ostat/gridfinity_extended_openscad/gridfinity_glue_stick.scad

include <modules/module_gridfinity_block.scad>
include <modules/gridfinity_constants.scad>

cup_height = 5;
stick_diameter = 30;
easement_z = 0.7; // a slightly large opening at the top for compliance while inserting.
minimum_wall = 4;

/* [Hidden] */
$fn = 64;
module end_of_customizer_opts() {}

blocks_needed = ceil((stick_diameter+2*minimum_wall)/env_pitch().x);

set_environment(
  width = 1,
  depth = 1,
  height = 2,
  render_position = "center")
glue_stick_cup(blocks_needed, blocks_needed, cup_height);

module glue_stick_cup(num_x=1, num_y=1, num_z=2) {
  difference() {
    grid_block(num_x, num_y, num_z,
      cupBase_settings = CupBaseSettings());
      translate([num_x*env_pitch().x/2, num_y*env_pitch().y/2, 0])
      glue_stick(num_z, stick_diameter);
  }
}

module glue_stick(num_z=5, diam) {
  floor_thickness = blocks_needed > 1 ? 5.5 : 1.2;
  translate([0, 0, floor_thickness]) cylinder(h=num_z*env_pitch().z, d=diam);
  translate([0, 0, (num_z - easement_z)*env_pitch().z + 1.2])
    cylinder(h=easement_z*env_pitch().z, d1=diam, d2=diam*1.1);
}
