ostat/gridfinity_extended_openscad/combined/gridfinity_baseplate.scad

///////////////////////////////////////
//Combined version of 'gridfinity_baseplate.scad'. Generated 2026-09-22 22:52
//Content hash 05C8F93E8DDB1E19475187FF5BAAC2B6E532E4B3174027AFBAF0A886D061BA3F
///////////////////////////////////////
// include instead of use, so we get the pitch

// Plate Style
Base_Plate_Options = "default";//[default:Efficient base, cnclaser:CNC or Laser cut]
// X dimension. grid units (multiples of 42mm) or mm.
Width = [3, 0]; //0.1
// Y dimension. grid units (multiples of 42mm) or mm.
Depth = [2, 0]; //0.1
oversize_method = "fill"; //[crop, fill]
position_fill_grid_x = "near";//[near:"← left", center:"↔ center", far:"→ right"]
position_fill_grid_y = "near";//[far:"↑ up", center:"↕ center", near:"↓ bottom"]
// X outer dimension. grid units (multiples of 42mm) or mm.
outer_Width = [0, 0]; //0.1
// Y outer dimension. grid units (multiples of 42mm) or mm.
outer_Depth = [0, 0]; //0.1
// z outer dimension. mm.
outer_Height = 0; //0.1
position_grid_in_outer_x = "center";//[near:"← left", center:"↔ center", far:"→ right"]
position_grid_in_outer_y = "center";//[far:"↑ up", center:"↕ center", near:"↓ bottom"]
//Reduce the frame wall size to this value
Reduced_Wall_Height = -1; //0.1
Reduced_Wall_Taper = false;
plate_corner_radius = 3.75; //0.01
//Corner radius for the inner corners (Works well with build_plate_enabled)
secondary_corner_radius = 3.75; //0.01

/* [Printer bed options] */
build_plate_enabled = "disabled";//[disabled, enabled, unique]
//spread out the plates, use if last row is small.
average_plate_sizes = false;
//Will split the plate in to the
build_plate_size = [200,250];

/* [Base Plate Options] */
// Enable magnets in the bin corner
Enable_Magnets = false;
//size of magnet, diameter and height. Zacks original used 6.5 and 2.4
Magnet_Size = [6.5, 2.4];  // .1
//raises the magnet, and creates a floor (for gluing)
Magnet_Z_Offset = 0;  // .1
//raises the magnet, and creates a ceiling to capture the magnet
Magnet_Top_Cover = 0;  // .1
// [Magnet Release Options]
// Method to help remove magnets: "none", "slot" (side pry), "hole" (poke from behind)
Magnet_Release_Method = "none"; //[none, slot, hole]
//Enable screws in the bin corner under the magnets
Corner_Screw_Enabled = false;
//Enable hold down screw in the center
Center_Screw_Enabled = false;
//Enable cavity to place frame weights
Enable_Weight = false;
//Removes the bottom taper
Remove_Bottom_Taper = false;

/* [Base Plate Clips]*/
Connector_Only = false;
Connector_Position = "center_wall"; //["center_wall","intersection","both"]

Connector_Clip_Enabled = false;
Connector_Clip_Size = 10;
Connector_Clip_Tolerance = 0.1;

//This feature is not yet finalised, or working properly.
Connector_Butterfly_Enabled = false;
Connector_Butterfly_Size = [5,4,1.5];
Connector_Butterfly_Radius = 0.1;
Connector_Butterfly_Tolerance = 0.1;

//This feature is not yet finalised, or working properly.
Connector_Filament_Enabled = false;
Connector_Filament_Diameter = 2;
Connector_Filament_Length = 8;

//This feature is not yet finalised, or working properly.
Connector_Snaps_Enabled = "disabled"; //["disabled","larger","smaller"]
Connector_Snaps_Clearance = 0.2;

/* [Custom Grid]*/
//Enable custom grid, you will configure this in the (Lid not supported)
Custom_Grid_Enabled = false;

//Custom gid sizes
//I am not sure it this is really useful, but its possible, so here we are.
//0:off the cell is off
//1:on the cell is on and all corners are rounded
//2-16, are bitwise values used to calculate what corners should be rounded, you need to subtract 2 from the value for the bitwise logic (so it does not clash with 0 and 1).
//[c,[x,y]], c corner value as shown above. [x,y] x and y size of the cell.
xpos1 = [3,[2,[3,3]],0,0,2,4,0];
xpos2 = [2,0,0,0,2,2,0];
xpos3 = [2,0,0,0,2,2,0];
xpos4 = [2,2,2,2,2,2,0];
xpos5 = [6,2,2,2,2,10,0];
xpos6 = [0,0,0,0,0,0,0];
xpos7 = [0,0,0,0,0,0,0];

/* [Model detail] */
//Work in progress,  Modify the default grid size. Will break compatibility
pitch = [42,42,7];  //[0:1:9999]
// minimum angle for a fragment (fragments = 360/fa).  Low is more fragments
fa = 6;
// minimum size of a fragment.  Low is more fragments
fs = 0.1;
// number of fragments, overrides $fa and $fs
fn = 0;

/* [debug] */
Render_Position = "center"; //[default,center,zero]
// Debug slice
cut = [0,0,0]; //0.1
// enable loging of help messages during render.
enable_help = false;

/* [Hidden] */
module end_of_customizer_opts() {}
//Combined from path gridfinity_constants.scad


// dimensions as declared on https://gridfinity.xyz/specification/

//Gridfinity grid size
gf_pitch = 42;
//Gridfinity height size
gf_zpitch = 7;

gf_taper_angle = 45;

// cup
gf_cup_corner_radius = 3.75;
gf_cup_floor_thickness = 0.7;  

// CupBase
gf_cupbase_lower_taper_height = 0.8;
gf_cupbase_riser_height = 1.8;
gf_cupbase_upper_taper_height = 2.15;
gf_cupbase_magnet_position = 4.8; 
gf_cupbase_screw_diameter = 3; 
gf_cupbase_screw_depth = 6;
gf_magnet_diameter = 6.5;
gf_magnet_thickness = 2.4;
gf_base_grid_clearance_height = 3.5;

//stacking lips
// Standard lip
// \        gf_lip_upper_taper_height 
//  |       gf_lip_riser_height
//   \      gf_lip_lower_taper_height
//    |     gf_lip_height
//   /      gf_lip_support_taper_height
//  /
// /
///
// Reduced lip
// \        gf_lip_upper_taper_height 
//  |       gf_lip_riser_height
// /        gf_lip_reduced_support_taper_height
/// 
gf_lip_lower_taper_height = 0.7;
gf_lip_riser_height = 1.8;
gf_lip_upper_taper_height = 1.9;
gf_lip_height = 1.2;
//gf_lip_support_taper_height = 2.5;
//gf_lip_reduced_support_taper_height = 1.9;

// base plate
gf_baseplate_lower_taper_height = 0.7;
gf_baseplate_riser_height = 1.8;
gf_baseplate_upper_taper_height = 2.15;
gf_baseplate_magnet_od = 6.5;
gf_baseplate_magnet_thickness = 2.4;

// top lip height 4.4mm
gf_Lip_Height = 4.4-0.6;//gf_lip_lower_taper_height + gf_lip_riser_height + gf_lip_upper_taper_height;

// cupbase height 4.75mm + 0.25.
function gfBaseHeight() = gf_cupbase_lower_taper_height + gf_cupbase_riser_height + gf_cupbase_upper_taper_height+0.25; //results in 5
gf_min_base_height = gfBaseHeight(); 

// base heighttop lip height 4.4mm
function gfBasePlateHeight() = gf_baseplate_lower_taper_height + gf_baseplate_riser_height + gf_baseplate_upper_taper_height;

 

// old names, that will get replaced
/*
gridfinity_lip_height = gf_Lip_Height; 
gridfinity_corner_radius = gf_cup_corner_radius ; 
gridfinity_zpitch = env_pitch().z;
minFloorThickness = gf_cup_floor_thickness;  
const_magnet_height = gf_magnet_thickness;
*/

//Small amount to add to prevent clipping in openSCAD
fudgeFactor = 0.01;

color_cup = "LightSlateGray";
color_divider = "Gainsboro"; //LemonChiffon
color_topcavity = "Green";//"SteelBlue";
color_label = "DarkCyan";
color_cupcavity = "LightGreen"; //IndianRed
color_wallcutout = "SandyBrown";
color_basehole = "DarkSlateGray";
color_base = "DimGray";
color_extension = "lightpink";
color_text = "Yellow"; //Gold
color_cut = "Black";
color_lid = "MediumAquamarine";
//CombinedEnd from path gridfinity_constants.scad
//Combined from path module_gridfinity_block.scad







show_gridfinity_demo = false;
if(show_gridfinity_demo){
  
  grid_block($fn=64);
 
  translate([50,0,0])
  union(){
    frame_cavity($fn=64);

    translate([0,50*3,0])
    frame_cavity(remove_bottom_taper=true,$fn=64);
    
    translate([0,50*4,0])
    frame_cavity(reducedWallHeight=1,$fn=64);
  }
  
  translate([150,0,0])
  union(){
    pad_oversize($fn=64);
    
    translate([0,50,0])
    pad_oversize(extend_down=5,$fn=64);
    
    translate([0,50*2,0])
    pad_oversize(margins=1,$fn=64);
    
    translate([0,50*3,0])
    pad_oversize(remove_bottom_taper=true,$fn=64);
    
    translate([0,50*4,0])
    pad_oversize(render_top=false,$fn=64);
    
    translate([0,50*5,0])
    pad_oversize(render_bottom=false,$fn=64);
  }  
}

// basic block with cutout in top to be stackable, optional holes in bottom
// start with this and begin 'carving'
//grid_block();
module grid_block(
  num_x=1, 
  num_y=2, 
  num_z=2, 
  position = "zero",
  filledin = "disabled", //[disabled, enabled, enabledfilllip]
  wall_thickness = 1.2,
  cupBase_settings = CupBaseSettings(),
  lip_settings = LipSettings(),
  help)
{
  lipHeight = 3.75;

  assert_openscad_version();
  cupBase_settings = ValidateCupBaseSettings(cupBase_settings);

  //Legacy variables.
  magnet_size=cupBase_settings[iCupBase_MagnetSize];
  screw_size=cupBase_settings[iCupBase_ScrewSize];
  hole_overhang_remedy=cupBase_settings[iCupBase_HoleOverhangRemedy];
  box_corner_attachments_only = cupBase_settings[iCupBase_CornerAttachmentsOnly];
  sub_pitch=cupBase_settings[iCupBase_SubPitch];
  flat_base=cupBase_settings[iCupBase_FlatBase];
  center_magnet_size = cupBase_settings[iCupBase_CenterMagnetSize];
    
  outer_size = [env_pitch().x - env_clearance().x, env_pitch().y - env_clearance().y];  // typically 41.5
  block_corner_position = [outer_size.x/2 - env_corner_radius(), outer_size.y/2 - env_corner_radius()];  // need not match center of pad corners

  magnet_position = calculateAttachmentPositions(magnet_size[iCylinderDimension_Diameter], screw_size[iCylinderDimension_Diameter]);
   
  overhang_fix = hole_overhang_remedy > 0 && magnet_size[iCylinderDimension_Diameter] > 0 && screw_size[iCylinderDimension_Diameter] > 0 ? hole_overhang_remedy : 0;
  overhang_fix_depth = 0.3;  // assume this is enough
  
  tz(env_pitch().z*num_z-fudgeFactor*2)
  if(filledin == "enabledfilllip"){
    color(env_colour(color_topcavity))
      tz(-fudgeFactor)
      hull() 
      cornercopy(block_corner_position, num_x, num_y) 
      cylinder(r=env_corner_radius(), h=lipHeight);
  } else {
    
    cupLip(
      num_x = num_x, 
      num_y = num_y, 
      lipStyle = lip_settings[iLipStyle],
      wall_thickness = wall_thickness,
      lip_notches = lip_settings[iLipNotch],
      lip_top_relief_height = lip_settings[iLipTopReliefHeight],
      lip_top_relief_width = lip_settings[iLipTopReliefWidth],
      lip_clip_position = lip_settings[iLipClipPosition],
      lip_non_blocking = lip_settings[iLipNonBlocking],
      align_grid = cupBase_settings[iCupBase_AlignGrid]);
  }
  
  translate(gridfinityRenderPosition(position,num_x,num_y))
  difference() {
    baseHeight = 5;
    intersection() {
      //Main cup outer shape
      color(env_colour(color_cup))
        tz(-fudgeFactor)
        hull() 
        cornercopy(block_corner_position, num_x, num_y) 
        cylinder(r=env_corner_radius(), h=env_pitch().z*num_z);

      union(){
        if(flat_base == FlatBase_rounded){
          basebottomRadius = let(fbr = cupBase_settings[iCupBase_FlatBaseRoundedRadius])
            fbr == -1 ? env_corner_radius()/2 : fbr;

          color(env_colour(color_cup))
          translate([env_clearance().x/2,env_clearance().y/2,0])
          roundedCube(
            x = num_x*env_pitch().x-env_clearance().x,
            y = num_y*env_pitch().y-env_clearance().y,
            z = env_pitch().z,
            size=[],
            topRadius = 0,
            bottomRadius = basebottomRadius,
            sideRadius = env_corner_radius(),
            centerxy = false,
            supportReduction_z = [cupBase_settings[iCupBase_FlatBaseRoundedEasyPrint],0]
            );
        } else {
          // logic for constructing odd-size grids of possibly half-pitch pads
          color(env_colour(color_base))
            pad_grid(
              num_x = num_x, 
              num_y = num_y, 
              sub_pitch = sub_pitch, 
              flat_base = flat_base, 
              cupBase_settings[iCupBase_MinimumPrintablePadSize],
              pitch=env_pitch(), 
              positionGridx = cupBase_settings[iCupBase_AlignGrid].x,
              positionGridy = cupBase_settings[iCupBase_AlignGrid].y);
        }

        color(env_colour(color_cup))
        tz(baseHeight) 
          cube([env_pitch().x*num_x, env_pitch().y*num_y, env_pitch().z*num_z]);
      }
    }
    
    color(env_colour(color_cup))
    bin_overhang_chamfer(
      num_x = num_x,
      num_y = num_y,
      baseHeight = baseHeight,
      wall_thickness = wall_thickness,
      corner_radius = env_corner_radius(),
      block_corner_position=block_corner_position,
      cupBase_settings = cupBase_settings);
   
    if(center_magnet_size[iCylinderDimension_Diameter]){
      //Center Magnet
      for(x =[0:1:num_x-1])
      {
        for(y =[0:1:num_y-1])
        {
          color(env_colour(color_basehole))
            translate([
               x * env_pitch().x + env_pitch().x / 2, // Add half pitch in X
               y * env_pitch().y + env_pitch().y / 2, // Add half pitch in Y
               -fudgeFactor
            ])
            cylinder(h=center_magnet_size[iCylinderDimension_Height]-fudgeFactor, d=center_magnet_size[iCylinderDimension_Diameter]);
        }
      }
    }
    
    color(env_colour(color_basehole))
    tz(-fudgeFactor)
    gridcopycorners(num_x, num_y, magnet_position, box_corner_attachments_only){
        magnet_rotation =
          $gcci[2] == [ 1, 1] ? 90 :
          $gcci[2] == [-1, 1] ? 180 :
          $gcci[2] == [-1,-1] ? 270 :
          $gcci[2] == [ 1,-1] ? 0 : 0;
        magnetCaptiveSideAccessSize = magnet_rotation == 0 || magnet_rotation == 180 
          ? env_pitch().x/2 - magnet_position.x 
          : env_pitch().y/2 - magnet_position.y;
        rotate([0,0,magnet_rotation-45])
        MagnetAndScrewRecess(
          magnetDiameter = magnet_size[iCylinderDimension_Diameter],
          magnetThickness = magnet_size[iCylinderDimension_Height]+0.1,
          screwDiameter = screw_size[iCylinderDimension_Diameter],
          screwDepth = screw_size[iCylinderDimension_Height],
          overhangFixLayers = overhang_fix,
          overhangFixDepth = overhang_fix_depth,
          easyMagnetRelease = cupBase_settings[iCupBase_MagnetEasyRelease] == MagnetEasyRelease_off ? false : 
                              cupBase_settings[iCupBase_MagnetCaptiveHeight] > 0 && cupBase_settings[iCupBase_MagnetSideAccess] == false ? false : true,
          magnetCaptiveHeight = cupBase_settings[iCupBase_MagnetCaptiveHeight],
          easyReleaseRotation = (cupBase_settings[iCupBase_NormalisedMagnetEasyRelease] == MagnetEasyRelease_outer ? 0 : 180),
          magnetRotation = magnet_rotation,
          enableSideAccess = cupBase_settings[iCupBase_MagnetSideAccess],
          magnetCaptiveSideAccessSize = [magnetCaptiveSideAccessSize, magnet_size[iCylinderDimension_Diameter], magnet_size[iCylinderDimension_Height]+0.1],
          magnetCrushDepth = cupBase_settings[iCupBase_MagnetCrushDepth],
          magnetChamfer = cupBase_settings[iCupBase_MagnetChamfer]
        );
    }
  }
 
  HelpTxt("grid_block",[
    "num_x",num_x
    ,"num_y",num_y
    ,"num_z",num_z
    ,"magnet_size",magnet_size
    ,"screw_size",screw_size
    ,"position",position
    ,"hole_overhang_remedy",hole_overhang_remedy
    ,"sub_pitch",sub_pitch
    ,"box_corner_attachments_only",box_corner_attachments_only
    ,"flat_base",flat_base
    ,"lipSettings",lip_settings
    ,"filledin",filledin]
    ,help);
}

//TODO: be better if we could round the corners of the chamfer around the bin.
module bin_overhang_chamfer(
  num_x,
  num_y,
  baseHeight,
  wall_thickness,
  corner_radius,
  block_corner_position,
  cupBase_settings = []){
  fudgeFactor = 0.01;

  alignGrid = cupBase_settings[iCupBase_AlignGrid];
  cavityFloorRadius = cupBase_settings[iCupBase_CavityFloorRadius];
  efficientFloor = cupBase_settings[iCupBase_EfficientFloor];
  sub_pitch = cupBase_settings[iCupBase_SubPitch];
  minimumPrintablePadSize = cupBase_settings[iCupBase_MinimumPrintablePadSize];

  calculate_bin_chamfer = function (
    width,
    pitch,
    clearance,
    wallThickness,
    cavityFloorRadius,
    efficientFloor,
    subPitch,
    minimumPrintablePadSize) 
    let(
      over_hanging_lip = (width*subPitch-floor(width*subPitch))/subPitch,
      over_hanging_lip_mm = (over_hanging_lip)*pitch-clearance/4,
      calculatedCavityFloorRadius = calculateCavityFloorRadius(cavityFloorRadius, wallThickness, efficientFloor),
      outer_wall_radius = calculatedCavityFloorRadius + wallThickness*2,
      large_h = sqrt(2 * outer_wall_radius ^ 2),
      small_h = (large_h - outer_wall_radius) * 2,
      max_chamfer = sqrt((small_h^2) / 2),
      correctable_lip = max(0, min(over_hanging_lip_mm, max_chamfer)))
    over_hanging_lip > 0 && over_hanging_lip < minimumPrintablePadSize ? correctable_lip : 0;

    chamfer_lip_x = calculate_bin_chamfer(
      width = num_x,
      pitch = env_pitch().x,
      clearance = env_clearance().x,
      wallThickness = wall_thickness,
      cavityFloorRadius = cavityFloorRadius,
      efficientFloor = efficientFloor,
      subPitch = sub_pitch,
      minimumPrintablePadSize = minimumPrintablePadSize
    );

    chamfer_lip_y = calculate_bin_chamfer(
      width = num_y,
      pitch = env_pitch().y,
      clearance = env_clearance().x,
      wallThickness = wall_thickness,
      cavityFloorRadius = cavityFloorRadius,
      efficientFloor = efficientFloor,
      subPitch = sub_pitch,
      minimumPrintablePadSize = minimumPrintablePadSize
    );

  chamfer_max= max(chamfer_lip_x, chamfer_lip_y);
  lower_radius = env_corner_radius() - chamfer_max;
  echo("bin_overhang_chamfer", num_x=num_x, num_y=num_y, chamfer_lip_x=chamfer_lip_x, chamfer_lip_y=chamfer_lip_y, chamfer_max=chamfer_max, lower_radius=lower_radius);
  if(chamfer_lip_x > 0 || chamfer_lip_y > 0)
  translate([0,0,baseHeight-fudgeFactor])
  difference() {
    cube([env_pitch().x*num_x, env_pitch().y*num_y, chamfer_max]);

    hull() 
      cornercopy(block_corner_position, num_x, num_y)
        union(){
          _translate = [
                cupBase_settings[iCupBase_AlignGrid].x == "far"
                  ? ($idx[0] == 0 ? -((-chamfer_lip_x)+env_clearance().x/4) : -env_clearance().x/4)
                  : ($idx[0] == 0 ? -env_clearance().x/4 : (-chamfer_lip_x)+env_clearance().x/4),
                cupBase_settings[iCupBase_AlignGrid].y == "far"
                  ? ($idx[1] == 0 ? -((-chamfer_lip_y)+env_clearance().y/4) : -env_clearance().y/4)
                  : ($idx[1] == 0 ? -env_clearance().y/4 : (-chamfer_lip_y)+env_clearance().y/4),
                -fudgeFactor];
        hull(){
            translate([0,0,chamfer_max+fudgeFactor*2])
            cylinder(r=env_corner_radius()+fudgeFactor, h=fudgeFactor);
            translate(_translate)
            cylinder(r=env_corner_radius()+fudgeFactor, h=fudgeFactor);
          }
        }
    
  }
}
//CombinedEnd from path module_gridfinity_block.scad
//Combined from path module_gridfinity.scad














module pad_grid(
  num_x, 
  num_y, 
  sub_pitch=1, 
  flat_base="off", 
  minimium_size = 0.2,
  pitch=env_pitch(), 
  positionGridx = "near", 
  positionGridy = "near") {
  assert(is_num(num_x));
  assert(is_num(num_y));
  assert(is_num(sub_pitch));
  assert(is_string(flat_base));
  assert(is_num(minimium_size));

  render_top = true;
  render_bottom = true;
  //echo("pad_grid", flat_base=flat_base, sub_pitch=sub_pitch, positionGridx=positionGridx, positionGridy=positionGridy, minimium_size=minimium_size);
  pad_copy(
    num_x = num_x, 
    num_y = num_y, 
    sub_pitch = sub_pitch, 
    flat_base = flat_base, 
    minimium_size = minimium_size,
    pitch=pitch, 
    positionGridx = positionGridx, 
    positionGridy = positionGridy)
      pad_oversize(
          $pad_copy_size.x, 
          $pad_copy_size.y,
          render_top=render_top,
          render_bottom=render_bottom);
}

// like a cylinder but produces a square solid instead of a round one
// specified 'diameter' is the side length of the square, not the diagonal diameter
module cylsq(d, h) {
  translate([-d/2, -d/2, 0]) cube([d, d, h]);
}

// like a tapered cylinder with two diameters, but square instead of round
module cylsq2(d1, d2, h) {
  linear_extrude(height=h, scale=d2/d1)
  square([d1, d1], center=true);
}

module frame_additives(
  num_x = 2, 
  num_y = 1, 
  position_fill_grid_x = "near",
  position_fill_grid_y = "near",
  render_top = true,
  render_bottom = true,
  remove_bottom_taper = false,
  extra_down=0, 
  frameLipHeight = 4,
  cornerRadius = gf_cup_corner_radius,
  reducedWallHeight = -1,
  reducedWallWidth = -1,
  reducedWallOuterEdgesOnly=false,
  enable_grippers = false) {

  assert(is_num(num_x));
  assert(is_num(num_y));
  assert(is_string(position_fill_grid_x));
  assert(is_string(position_fill_grid_y));
  assert(is_bool(render_top));
  assert(is_bool(render_bottom));
  assert(is_bool(remove_bottom_taper));
  assert(is_num(extra_down));
  assert(is_num(frameLipHeight));
  assert(is_num(cornerRadius));
  assert(is_num(reducedWallHeight));
  assert(is_num(reducedWallWidth));
  assert(is_bool(reducedWallOuterEdgesOnly));
  assert(is_bool(enable_grippers));

  frameWallReduction = reducedWallHeight >= 0 ? max(0, frameLipHeight-reducedWallHeight) : -1;
  if(env_help_enabled("debug")) echo("frame_addatives", childres = $children);
      
    translate([0, 0, -fudgeFactor]) 
      gridcopy(
        num_x, 
        num_y,
        positionGridx = position_fill_grid_x,
        positionGridy = position_fill_grid_y) {
      if($gc_size.x > 0.2 && $gc_size.y >= 0.2){
        
        //wall reducers, cutouts and clips
        children();
    }
  }
}


module frame_cavity(
  num_x = 2, 
  num_y = 1, 
  position_fill_grid_x = "near",
  position_fill_grid_y = "near",
  render_top = true,
  render_bottom = true,
  remove_bottom_taper = false,
  extra_down=0, 
  frameLipHeight = 4,
  cornerRadius = gf_cup_corner_radius,
  reducedWallHeight = -1,
  reducedWallWidth = -1,
  reducedWallOuterEdgesOnly=false,
  enable_grippers = false) {

  assert(is_num(num_x));
  assert(is_num(num_y));
  assert(is_string(position_fill_grid_x));
  assert(is_string(position_fill_grid_y));
  assert(is_bool(render_top));
  assert(is_bool(render_bottom));
  assert(is_bool(remove_bottom_taper));
  assert(is_num(extra_down));
  assert(is_num(frameLipHeight));
  assert(is_num(cornerRadius));
  assert(is_num(reducedWallHeight));
  assert(is_num(reducedWallWidth));
  assert(is_bool(reducedWallOuterEdgesOnly));
  assert(is_bool(enable_grippers));

  frameWallReduction = reducedWallHeight >= 0 ? max(0, frameLipHeight-reducedWallHeight) : -1;

    translate([0, 0, -fudgeFactor]) 
      gridcopy(
        num_x, 
        num_y,
        positionGridx = position_fill_grid_x,
        positionGridy = position_fill_grid_y) {
      if($gc_size.x > 0.2 && $gc_size.y >= 0.2){
        if(frameWallReduction>=0)
          for(side=[[0, [$gc_size.x, $gc_size.y]*env_pitch().x, "x"],[90, [$gc_size.y, $gc_size.x]*env_pitch().y, "y"]]){
            if(side[1].x >= env_pitch().x/2)
            if(!reducedWallOuterEdgesOnly || ($gc_is_corner[1] && side[2] =="x") || ($gc_is_corner[0] && side[2] =="y"))
            translate([$gc_size.x/2*env_pitch().x,$gc_size.y/2*env_pitch().y,frameLipHeight])
            rotate([0,0,side[0]])
              WallCutout(
                lowerWidth=side[1].x-(reducedWallWidth > 0 ? reducedWallWidth*2 : 20),
                wallAngle=80,
                height=frameWallReduction,
                thickness=side[1].y+fudgeFactor*2,
                cornerRadius=frameWallReduction,
                topHeight=1);
              }

      //wall reducers, cutouts and clips
      if($children >=2) children(1);

      pad_oversize(
        num_x=$gc_size.x,
        num_y=$gc_size.y,
        margins=1,
        extend_down=extra_down,
        render_top=render_top,
        render_bottom=render_bottom,
        remove_bottom_taper=remove_bottom_taper)
          //cell cavity
          if($children >=1) children(0);
    }
  }
}

// unit pad slightly oversize at the top to be trimmed or joined with other feet or the rest of the model
// also useful as cutouts for stacking
//pad_oversize(margins=1,extend_down=5, $fn=64);
module pad_oversize(
  num_x=1, 
  num_y=1, 
  margins=0,
  render_top = true,
  render_bottom = true,
  remove_bottom_taper = false,
  extend_down = 0) {
  
  assert(!is_undef(num_x), "num_x is undefined");
  assert(is_num(num_x), "num_x must be a number");
  assert(!is_undef(num_y), "num_y is undefined");
  assert(is_num(num_y), "num_y must be a number");
  assert(!is_undef(margins), "margins is undefined");
  assert(is_num(margins), "margins must be a number >= 0");
  assert(!is_undef(extend_down), "extend_down is undefined");
  assert(is_num(extend_down), "extend_down must be a number >= 0");
  
  if(env_help_enabled("trace")) echo("pad_oversize", num_x=num_x, num_y=num_y, margins= margins);

  // pad_corner_position = [env_pitch().x/2 - 4,env_pitch().y/2 - 4]; 
  // must be 17 to be compatible
  pad_corner_position = [
    env_pitch().x/2-env_corner_radius()-env_clearance().x/2, 
    env_pitch().y/2-env_corner_radius()-env_clearance().y/2];

  bevel1_top = 0.8;     // z of top of bottom-most bevel (bottom of bevel is at z=0)
  bevel2_bottom = 2.6;  // z of bottom of second bevel
  bevel2_top = 5;       // z of top of second bevel
  bonus_ht = 0.2;       // extra height (and radius) on second bevel
  
  // female parts are a bit oversize for a nicer fit
  radialgap = margins ? 0.25 : 0;  // oversize cylinders for a bit of clearance
  //axialdown = margins ? 0.1 : 0;   // a tiny bit of axial clearance present in Zack's design
  //remove axialdown as it messes up the placement of the attachements 
  axialdown =0;
  fudgeFactor = 0.01;
  
  translate([0, 0, -axialdown])
  difference() {
    union() {
      //top over size taper
      if(render_top){
        hull() cornercopy(pad_corner_position, num_x, num_y) {
          if (sharp_corners) {
            translate(bevel2_bottom) 
            cylsq2(d1=(env_corner_radius()-2.15+radialgap)*2, d2=(env_corner_radius()+0.25+radialgap+bonus_ht)*2, h=bevel2_top-bevel2_bottom+bonus_ht);
          }
          else {
            tz(bevel2_bottom) 
            cylinder(d1=(env_corner_radius()-2.15+radialgap)*2, d2=(env_corner_radius()+0.25+radialgap+bonus_ht)*2, h=bevel2_top-bevel2_bottom+bonus_ht);
          }
        }
      }
      
      if(render_bottom){ 
        hull()
        cornercopy(pad_corner_position, num_x, num_y) {
          if (sharp_corners) {
            cylsq(d=1.6+2*radialgap, h=0.1);
            translate([0, 0, bevel1_top]) 
            cylsq(d=(env_corner_radius()-2.15+radialgap)*2, h=1.9+bevel2_top-bevel2_bottom+bonus_ht);
          }
          else {
            cylinder(d=remove_bottom_taper ? (env_corner_radius()-2.15+radialgap)*2 : 1.6+2*radialgap, h=0.1);
            translate([0, 0, bevel1_top]) 
              cylinder(d=(env_corner_radius()-2.15+radialgap)*2, h=1.9+bevel2_top-bevel2_bottom+bonus_ht);
          }
        }
      }
 
      if(extend_down > 0)
      translate([0,0,-extend_down])
      difference(){
        hull() 
        cornercopy(pad_corner_position, num_x, num_y) {
          if (sharp_corners) {
            cylsq(d=1.6+2*radialgap, h=extend_down+fudgeFactor);
          }
          else {
            cylinder(d=1.6+2*radialgap, h=extend_down+fudgeFactor);
          }
        }
        //for baseplate patterns
        children();
      }
    }
    
    // cut off bottom if we're going to go negative
    if (margins && extend_down == 0) {
      cube([env_pitch().x*num_x, env_pitch().y*num_y, axialdown]);
    }
  }
}
 
module pad_copy(
  num_x, num_y, 
  sub_pitch=1, 
  flat_base="off", 
  minimium_size = 0.2,
  pitch=env_pitch(), 
  positionGridx = "near", 
  positionGridy = "near") {
  assert(is_num(num_x));
  assert(is_num(num_y));
  assert(is_num(sub_pitch));
  assert(is_string(flat_base));
  assert(is_num(minimium_size));

  if(env_help_enabled("debug")) echo("pad_copy", flat_base=flat_base, sub_pitch=sub_pitch, minimium_size=minimium_size);
 
  if (flat_base != FlatBase_off) {
    $pad_copy_size = [num_x, num_y];
    if(env_help_enabled("debug")) echo("pad_grid_flat_base", pad_copy_size=$pad_copy_size);
    if($pad_copy_size.x >= minimium_size && $pad_copy_size.y >= minimium_size) {
      children();
    }
  }
  else if (sub_pitch > 1) {
    gridcopy(
      num_x=num_x*sub_pitch, 
      num_y=num_y*sub_pitch, 
      pitch=[pitch.y/sub_pitch,pitch.x/sub_pitch,pitch.z],
      positionGridx = positionGridx, 
      positionGridy = positionGridy) {
      $pad_copy_size = $gc_size/sub_pitch;
      if(env_help_enabled("debug")) echo("pad_grid_sub_pitch", gci=$gci, gc_size=$gc_size, pad_copy_size=$pad_copy_size);
      if($pad_copy_size.x >= minimium_size && $pad_copy_size.y >= minimium_size) {
         children();      }
    }
  }
  else {
    gridcopy(
      num_x=num_x, 
      num_y=num_y, 
      pitch=pitch,
      positionGridx = positionGridx, 
      positionGridy = positionGridy) {
      $pad_copy_size = $gc_size;
      if(env_help_enabled("debug")) echo("pad_grid", gci=$gci, gc_size=$gc_size, pad_copy_size=$pad_copy_size);
      if($pad_copy_size.x >= minimium_size && $pad_copy_size.y >= minimium_size) {
        children();
      }
    }
  }
}

// make repeated copies of something(s) at the gridfinity spacing of 42mm
module gridcopy(
  num_x, 
  num_y, 
  pitch=env_pitch(), 
  positionGridx = "near", 
  positionGridy = "near") {
  assert(is_num(num_x) && num_x>=0, "num_x must be a number greater than 1");
  assert(is_num(num_y) && num_y>=0, "num_y must be a number greater than 1");
  assert(is_list(pitch));
  
  function num_to_list(num, positionGrid = "near") = 
    let(
      centerGrid = positionGrid == "center",
      padding = ceil(num) != num ? (num - floor(num))/(centerGrid?2:1) : 0,
      count = ceil(num) + ((padding > 0 && centerGrid) ? 1 :0),
      hasPrePad = padding != 0 && (positionGrid == "center" || positionGrid == "far"),
      hasPostPad = padding != 0 && (positionGrid == "center" || positionGrid == "near"))
      [for (i = [ 0 : count - 1 ]) 
        i == 0 && hasPrePad ? [padding,false]
          : i == count-1 && hasPostPad ? [padding,false]
          : [1, 
            (i == 0 && !hasPrePad) ||
            (i == 1 && hasPrePad) ||
            (i == (count-1) && !hasPostPad) ||
            (i == (count-2) && hasPostPad)]];    
    
  xCellsList = num_to_list(num_x, positionGridx);
  yCellsList = num_to_list(num_y, positionGridy);
  
  $gc_count=[len(xCellsList), len(yCellsList)];
  
  if(env_help_enabled("debug")) echo("gridcopy", xCellsList=xCellsList, yCellsList=yCellsList);
  
  for (xi=[0:len(xCellsList)-1]) 
    for (yi=[0:len(yCellsList)-1])
    {
      $gci=[xi,yi,0];
      $gc_count=[len(xCellsList), len(yCellsList), 0];
      $gc_size=[xCellsList[xi][0], yCellsList[yi][0], 0];
      //is this a corner really means is outer edge.
      $gc_is_corner=[xCellsList[xi][1], yCellsList[yi][1]];
      $gc_position=[
        vector_sum(xCellsList, 0, xi,0)-xCellsList[xi][0], 
        vector_sum(yCellsList, 0, yi,0)-yCellsList[yi][0], 0];
      translate([$gc_position.x*pitch.x,$gc_position.y*pitch.y,0])
        children();
    }
}         
  
// similar to cornercopy, can only copy to box corners
// r, position of the corner from the center for a full sized. Must be less than half of pitch (normally 17 for gridfinity) .
// num_x, num_y, size of the cube in units of pitch.
// pitch, size of one unit.
// center, center the grid
// reverseAlignment, reverse the alignment of the corners
module gridcopycorners(
  num_x, 
  num_y, 
  r, 
  onlyBoxCorners = false, //enabled, disabled, aligned
  pitch=env_pitch(), 
  center = false, 
  reverseAlignment=[false,false]) {
  assert(is_list(pitch), "pitch must be a list");
  assert(is_list(r), "pitch must be a list");
  assert(is_num(num_x), "num_x must be a number");
  assert(is_num(num_y), "num_y must be a number");
  r = is_num(r) ? [r,r] : r;
  
  onlyBoxCornersEnabled = is_bool(onlyBoxCorners) ? onlyBoxCorners :
    is_string(onlyBoxCorners) ? (onlyBoxCorners == "enabled" || onlyBoxCorners == "aligned") : false;
  onlyBoxCornersAligned = onlyBoxCorners == "aligned";

  cornerMultiplier = onlyBoxCornersAligned ? 1 : 2;

  translate(center ? [0,0] : [pitch.x/2,pitch.y/2])
  for (cellx=[1:ceil(num_x)], celly=[1:ceil(num_y)]) 
    for (quadrentx=[-1, 1], quadrenty=[-1, 1]) {
      cell = [cellx, celly];
      quadrent = [quadrentx, quadrenty];
      gridPosition = [cell.x+(quadrent.x == -1 ? -0.5 : 0), cell.y+(quadrent.y == -1 ? -0.5 : 0)];
      trans = [pitch.x*(cell.x-1)+quadrent.x*r.x, pitch.y*(cell.y-1)+ quadrent.y*r.y, 0];
      $gcci=[trans,cell,quadrent];

      cornerVisible = 
        (!reverseAlignment.x && gridPosition.x <= num_x || reverseAlignment.x && 1.5-gridPosition.x <= num_x) && 
        (!reverseAlignment.y && gridPosition.y <= num_y || reverseAlignment.y && 1.5-gridPosition.y <= num_y);
      if(env_help_enabled("debug")) echo("gridcopycorners", num_x=num_x,num_y=num_y, gcci=$gcci, gridPosition=gridPosition, reverseAlignment=reverseAlignment, cornerVisible=cornerVisible);
      //only copy if the cell is atleast half size
      if(cornerVisible)
        //only box corners or every cell corner
        if(!onlyBoxCornersEnabled || 
          ((cell.x == 1 && quadrent.x == -1) && (cell.y == 1  && quadrent.y == -1)) ||
          (gridPosition.x*cornerMultiplier == floor(num_x*cornerMultiplier) && gridPosition.y*cornerMultiplier == floor(num_y*cornerMultiplier)) ||
          ((cell.x == 1 && quadrent.x == -1) && gridPosition.y*cornerMultiplier == floor(num_y*cornerMultiplier) ) ||
          (gridPosition.x*cornerMultiplier == floor(num_x*cornerMultiplier) && (cell.y == 1 && quadrent.y == -1))) 
          translate(trans)
          children();
    }
}

// Coppies the children to the corners to create a square shape
// r, position of the corner from the center for a full sized. Must be less than half of pitch (normally 17 for gridfinity) .
// num_x, num_y, size of the cube in units of pitch.
// pitch, size of one unit.
// num_x = 1 give r*2, num_x = 2 give r*2+pitch, 
// similar to quadtranslate but expands to extremities of a block
module cornercopy(r, num_x=1, num_y=1,pitch=env_pitch(), center = false) {
  assert(!is_undef(r), "r is undefined");
  assert(is_list(pitch), "pitch must be a list");
  assert(is_num(num_x), "num_x must be a number");
  assert(is_num(num_y), "num_y must be a number");
  r = is_num(r) ? [r,r] : r;

  translate(center ? [0,0] : [pitch.x/2,pitch.y/2])
  for (xx=[0, 1], yy=[0, 1]) {
    $idx=[xx,yy,0];
    xpos = xx == 0 ? -r.x : max(pitch.x*(num_x-1)+r.x,-r.x);
    ypos = yy == 0 ? -r.y : max(pitch.y*(num_y-1)+r.y,-r.y);
    if(env_help_enabled("debug")) echo("cornercopy", num_x=num_x,num_y=num_y,pitch=pitch, center=center, idx=$idx, gridPosition=[xpos,ypos,0]);
    translate([xpos, ypos, 0]) 
      children();
  }
}

module debug_cut(cutx, cuty, cutz) {
  cutx = is_undef(cutx) ? env_cutx() : cutx;
  cuty = is_undef(cuty) ? env_cuty() : cuty;
  cutz = is_undef(cutz) ? env_cutz() : cutz;
  
  num_x = env_numx();
  num_y = env_numy();
  num_z = env_numz();
  
  difference(){
    children();
    
    if((cutx != 0 || cuty != 0 || cutz != 0) && $preview){
      echo("debug_cut is enabled", cutx=cutx, cuty=cuty, cutz=cutz);

      //Render the cut, used for debugging
      if(cutx != 0 && $preview){
        color(color_cut)
        translate(cutx > 0 
          ? [-fudgeFactor,-fudgeFactor,-fudgeFactor]
          : [(num_x-abs(cutx))*env_pitch().x-fudgeFactor,-fudgeFactor,-fudgeFactor])
        translate([-fudgeFactor,-fudgeFactor,-fudgeFactor])
          cube([
              abs(cutx)*env_pitch().x, 
              num_y*env_pitch().y+fudgeFactor*2,
              (num_z+1)*env_pitch().z+fudgeFactor*2]);
      }
      if(cuty != 0 && $preview){
        color(color_cut)
        translate(cuty > 0 
          ? [-fudgeFactor,-fudgeFactor,-fudgeFactor]
          : [-fudgeFactor,(num_y-abs(cuty))*env_pitch().y-fudgeFactor,-fudgeFactor])
          cube([
            num_x*env_pitch().x+fudgeFactor*2,
            abs(cuty)*env_pitch().y,
            (num_z+1)*env_pitch().z+fudgeFactor*2]);
      }
      if(cutz != 0 && $preview){
        color(color_cut)
        translate(cutz > 0 
          ? [-fudgeFactor,-fudgeFactor,-fudgeFactor]
          : [-fudgeFactor,-fudgeFactor,(num_z+1-abs(cutz))*env_pitch().z-fudgeFactor]
          )
          cube([
            num_x*env_pitch().x+fudgeFactor*2,
            num_y*env_pitch().y+fudgeFactor*2,
            abs(cutz)*env_pitch().z]);
      }
    }
  }
}
//CombinedEnd from path module_gridfinity.scad
//Combined from path ub_helptxt.scad



// works from OpenSCAD version 2021 or higher   maintained at https://github.com/UBaer21/UB.scad

/** \mainpage
 * ##Open SCAD library www.openscad.org 
 * **Author:** ulrich.baer+UBscad@gmail.com (mail me if you need help - i am happy to assist)
*/


// display the module variables in a copyable format
module HelpTxt(titel,string,help){ 
  help=is_undef(help)?is_undef($helpM)?false:
                                $helpM:
  help;
  idxON=is_undef($idxON)?false:$idxON?true:false;
  idx=is_undef($idx)||idxON?false:is_list($idx)?norm($idx):$idx;
  
   joinArray= function(in,out="",pos=0) pos>=len(in)?out:
        joinArray(in=in,out=str(out,in[pos]),pos=pos +1); 

helpText=[for(i=[0:2:len(string)-1])str(string[i],"=",string[i+1],",\n  ")];
 if(version()[0]<2021){ 
if(help)if(is_list(string))echo(
    
str("<H3> <font color=",helpMColor,"> Help ",titel, "(",
    helpText[0]
,helpText[1]?helpText[1]:""
,helpText[2]?helpText[2]:""
,helpText[3]?helpText[3]:""
,helpText[4]?helpText[4]:""
,helpText[5]?helpText[5]:""
,helpText[6]?helpText[6]:""
,helpText[7]?helpText[7]:""
,helpText[8]?helpText[8]:""
,helpText[9]?helpText[9]:""
,helpText[10]?helpText[10]:""
,helpText[11]?helpText[11]:""
,helpText[12]?helpText[12]:""
,helpText[13]?helpText[13]:""
,helpText[14]?helpText[14]:""
,helpText[15]?helpText[15]:""
,helpText[16]?helpText[16]:""
,helpText[17]?helpText[17]:""
,helpText[18]?helpText[18]:""
,helpText[19]?helpText[19]:""
,helpText[20]?helpText[20]:"" 
,helpText[21]?helpText[21]:""
,helpText[22]?helpText[22]:""
,helpText[23]?helpText[23]:""
,helpText[24]?helpText[24]:""
,helpText[25]?helpText[25]:""
,helpText[26]?helpText[26]:""
,helpText[27]?helpText[27]:""
,helpText[28]?helpText[28]:""
,helpText[29]?helpText[29]:""


// ," name=",name,
," help);"));  
else HelpTxt("Help",["titel",titel,"string",["string","data","help",help],"help",help],help=1);
}
else{ // current versions help 
if(help&&!idx)if(is_list(string))echo(
    
str("🟪\nHelp ",titel, "(\n  ",
joinArray(helpText)
,"help=",help,"\n);\n"));    
else HelpTxt("Help",["titel",titel,"string",string,"help",help],help=1);
}
}
//CombinedEnd from path ub_helptxt.scad
//Combined from path ub_common.scad


// works from OpenSCAD version 2021 or higher   maintained at https://github.com/UBaer21/UB.scad

/** \mainpage
 * ##Open SCAD library www.openscad.org 
 * **Author:** ulrich.baer+UBscad@gmail.com (mail me if you need help - i am happy to assist)
*/

useVersion=undef;

co=[
["silver","lightgrey","darkgrey","grey","slategrey","red","orange","lime","cyan","lightblue","darkblue","purple",[.8,.8,.8,.3],[.8,.8,.8,.6],"cyan","magenta","yellow","black","white","red","green","blue",[0.77,0.75,0.72]],//std
["White","Yellow","Magenta","Red","Cyan","Lime","Blue","Gray","Silver","Olive","Purple","Maroon","Teal","Green","Navy","Black"],//VGA
["Gainsboro","LightGray","Silver","DarkGray","Gray","DimGray","LightSlateGray","SlateGray","DarkSlateGray","Black"],//grey
["Pink","LightPink","HotPink","DeepPink","PaleVioletRed","MediumVioletRed"],//pink
["LightSalmon","Salmon","DarkSalmon","LightCoral","IndianRed","Crimson","Firebrick","DarkRed","Red"],//red
["OrangeRed","Tomato","Coral","DarkOrange","Orange"],//orange
["Yellow","LightYellow","LemonChiffon","LightGoldenrodYellow","PapayaWhip","Moccasin","PeachPuff","PaleGoldenrod","Khaki","DarkKhaki","Gold"],//yellows
["Cornsilk","BlanchedAlmond","Bisque","NavajoWhite","Wheat","Burlywood","Tan","RosyBrown","SandyBrown","Goldenrod","DarkGoldenrod","Peru","Chocolate","SaddleBrown","Sienna","Brown","Maroon"],//browns
["DarkOliveGreen","Olive","OliveDrab","YellowGreen","LimeGreen","Lime","LawnGreen","Chartreuse","GreenYellow","SpringGreen","MediumSpringGreen","LightGreen","PaleGreen","DarkSeaGreen","MediumAquamarine","MediumSeaGreen","SeaGreen","ForestGreen","Green","DarkGreen"],//greens
["Cyan","LightCyan","PaleTurquoise","Aquamarine","Turquoise","MediumTurquoise","DarkTurquoise","LightSeaGreen","CadetBlue","DarkCyan","Teal"],//cyans
["LightSteelBlue","PowderBlue","LightBlue","SkyBlue","LightSkyBlue","DeepSkyBlue","DodgerBlue","CornflowerBlue","SteelBlue","RoyalBlue","Blue","MediumBlue","DarkBlue","Navy","MidnightBlue"],//blue
["Lavender","Thistle","Plum","Violet","Orchid","Magenta","MediumOrchid","MediumPurple","BlueViolet","DarkViolet","DarkOrchid","DarkMagenta","Purple","Indigo","DarkSlateBlue","SlateBlue","MediumSlateBlue"],//violetts
["White","Snow","Honeydew","MintCream","Azure","AliceBlue","GhostWhite","WhiteSmoke","Seashell","Beige","OldLace","FloralWhite","Ivory","AntiqueWhite","Linen","LavenderBlush","MistyRose"],//white
["Red","darkorange","Orange","Yellow","Greenyellow","lime","limegreen","turquoise","cyan","deepskyblue","dodgerblue","Blue","Purple","magenta"],//rainbow
["magenta","Purple","Blue","dodgerblue","deepskyblue","cyan","turquoise","limegreen","lime","Greenyellow","Yellow","Orange","darkorange","Red","darkorange","Orange","Yellow","Greenyellow","lime","limegreen","turquoise","cyan","deepskyblue","dodgerblue","Blue","Purple"]//rainbow2
];

styles=[

"Condensed",
"Condensed Oblique",
"Condensed Bold",
"Condensed Bold Oblique",
"Condensed Bold Italic",
"SemiCondensed",
"SemiLight Condensed",
"SemiLight SemiCondensed",
"SemiBold SemiCondensed",
"SemiBold Condensed",
"Light Condensed",
"Light SemiCondensed",
"SemiLight",
"Light",
"ExtraLight",
"Light Italic",
"Bold",
"Bold SemiCondensed",
"Semibold",
"Semibold Italic",
"Bold Italic",
"Bold Oblique",
"Black",
"Black Italic",
"Book",
"Regular",
"Italic",
"Medium",
"Oblique",
];

needs2D=["Rand","WKreis","Welle","Rund","Rundrum", "LinEx", "RotEx","SBogen","Bogen","HypKehle","Roof"]; /// modules needing 2D children 

function bool(n,bool)= b(n,bool);
function b(n,bool)=  is_list(n)?[for(i=[0:len(n)-1])b(n[i],bool)]:
                               is_num(n)?bool||is_undef(bool)?n?true:
                                                                false:
                                                              n?n:
                                                                0:
                                         bool?n?true:  // n = bool
                                                false:
                                              n?1:
                                                0;



function v3(v)= [
is_num(v.x)?v.x:is_num(v)?v:0,
is_num(v.y)?v.y:0,
is_num(v.z)?v.z:0,
 ];

function gradB(b,r)=360/(PI*r*2)*b; // winkel zur Bogen strecke b des Kreisradiuses r

// list of parent modules [["name",id]]
function parentList(n=-1,start=1)=  is_undef($parent_modules)||$parent_modules==start?undef:[for(i=[start:$parent_modules +n])[parent_module(i),i]];

function is_parent(parent= needs2D, i= 0)=
is_list(parent)?is_num(search(parent,parentList())[i])?true:
                                                      i<len(parent)-1?is_parent(parent=parent,i=i+1):
                                                                      false:
                is_num(search([parent],parentList())[0]);

/** \name stringChunk
\page Functions
stringChunk() separates charcter from a string
\param txt input string
\param start start of extraction
\param length number of characters to extract
*/
function stringChunk(txt,start=0,length,string="")=
  let(
    start=abs(start),
    length=is_undef(length)?len(str(txt))-start:length
  )
  len(string)<length&&start<len(txt)?stringChunk(txt=txt,length=length,start=start+1,string=str(string,str(txt)[start])):string;


/// display variable values
module InfoTxt(name,string,info,help=false){
  $tab=is_undef($tab)?0:$tab;
  info=is_undef(info)?is_undef($info)?false:
                                $info:
  info;
  
  //  https://en.wikibooks.org/wiki/OpenSCAD_User_Manual/User-Defined_Functions_and_Modules#Function_Literals
 noInfo=is_undef($noInfo)?false:$noInfo; 
 idx=is_undef($idx)?false:is_list($idx)?norm($idx):$idx;
 idxON=is_undef($idxON)?false:$idxON?true:false;
 joinArray= function(in,out="",pos=0) pos>=len(in)?out: // scad version > 2021
        joinArray(in=in,out=str(out,in[pos]),pos=pos +1);   
    
 if(version()[0]<2021){   
  infoText=[for(i=[0:2:len(string)-1])str(string[i],"=",is_num(string[i+1])?negRed(string[i+1]):string[i+1],i<len(string)-2?", ":"")];
      
if(info)if(is_list(string))echo( 
 str(is_bool(info)?"":"<b>",info," ",name," ", 
infoText[0]
,infoText[1]?infoText[1]:""
,infoText[2]?infoText[2]:""
,infoText[3]?infoText[3]:""
,infoText[4]?infoText[4]:""
,infoText[5]?infoText[5]:""
,infoText[6]?infoText[6]:""
,infoText[7]?infoText[7]:""
,infoText[8]?infoText[8]:""
,infoText[9]?infoText[9]:""
));
else HelpTxt(titel="InfoTxt",string=["name",name,"string","[text,variable]","info",info],help=1);
}
else { // current version info
  infoText=[for(i=[0:2:len(string)-1])str(string[i],"=",string[i+1],i<len(string)-2?", ":"")];
      
if(info&&(!idx||idxON)&&!noInfo)if(is_list(string))echo( 
 str(is_string(info)?$tab?"⏩\t":
                          "🟩\t••":
                     "",$tab?" ╞▷   ":
                             "",b($tab,false)>1?" ┗▶   ":
                                                " ",info," ",name," ",
joinArray(infoText)));

else HelpTxt(titel="InfoTxt",string=["name",name,"string","[text,variable]","info",info],help=1);
}
HelpTxt(titel="InfoTxt",string=["name",name,"string","[text,variable]","info",info],help=help);
}

/// missing object text
module MO(condition=true,warn=false){
$idx=is_undef($idx)?false:$idx;
Echo(str(parent_module(2)," has no children!"),color=warn?"warning":"red",condition=condition&&$parent_modules>1&&!$idx,help=false);    
}

/// short for translate[];
module T(x=0,y=0,z=0,help=false)
{
    //translate([x,y,z])children();
if(is_list(x))
    multmatrix(m=[
    [1,0,0,x[0]],
    [0,1,0,x[1]],    
    [0,0,1,is_undef(x.z)?z:x[2]+z],
    [0,0,0,1]    
    ])children(); 
else
    multmatrix(m=[
    [1,0,0,x],
    [0,1,0,y],    
    [0,0,1,z],
    [0,0,0,1]    
    ])children(); 


    MO(!$children);
    HelpTxt("T",["x",x,"y",y,"z",z],help);
}

module Text(text="»«",size=5,h,cx,cy,cz,center=0,spacing=1,fn,fs=$fs,radius=0,rot=[0,0,0],font="Bahnschrift:style=bold",style,help,name,textmetrics=true,viewPos=false,trueSize="body")
{

text=str(text);
lenT=len(text);
textmetrics=version()[0]<2022?false:textmetrics;

Echo(str("Sizing inactive trueSize=",trueSizeSW),color="warning",condition=trueSize!="size"&&( (!textmetrics&&trueSize!="body")||(is_num(useVersion)&&useVersion<22.208) ) );

trueSizeSW=is_num(useVersion)&&useVersion<22.208?"size":trueSize;
inputSize=size;

style=is_string(style)?style:styles[style];
font=is_num(font)?fonts[font]:font;
fontstr=is_undef(style)?font:str(font,":style=",style);

hp=textmetrics?textmetrics(text="hpbdlq",font=fontstr,size=1,spacing=spacing).size.y:1;
cap=textmetrics?textmetrics(text="HTAME",font=fontstr,size=1,spacing=spacing).size.y:1;
textSize=textmetrics?textmetrics(text=text,font=fontstr,size=1,spacing=spacing).size:[lenT*spacing,1];
fontS=textmetrics?fontmetrics(font=fontstr,size=1).nominal:1;


size=trueSizeSW=="body"?size*.72:
     trueSizeSW=="hp"?size/hp:
     trueSizeSW=="cap"?size/cap:
     trueSizeSW=="text"?size/textSize.y:
     trueSizeSW=="textl"?size/textSize.x:
     trueSizeSW=="font"?size/(fontS.ascent-fontS.descent):
     size;

    h=is_parent(needs2D)?0:is_undef(h)?size:h;
    cx=center?is_undef(cx)?1:cx:is_undef(cx)?0:cx;
    cy=center?is_undef(cy)?1:cy:is_undef(cy)?0:cy;
    cz=center?is_undef(cz)?1:cz:is_undef(cz)?0:cz;

    
    
    txtSizeX=textmetrics?textmetrics(text=text,font=fontstr,size=size,spacing=spacing).size.x:size*spacing*lenT;
    txtSizeY=textmetrics?textmetrics(text=text,font=fontstr,size=size,spacing=spacing).size.y:size;
    fontSize=[for(i=[0:max(lenT-1,0)])textmetrics?
      textmetrics(text=stringChunk(txt=text,length=i),font=fontstr,size=size,spacing=spacing).advance.x + textmetrics(text=text[i],font=fontstr,size=size,spacing=1).advance.x/2*(cx?1:1)
      :
      (size*spacing)*i];
      

 valign=cy?b(cy,false)<0?"bottom":
                         b(cy,false)>1?"top":
                                       "center":
           "baseline";
           
 halign=bool(cx,false)>0?"center"
                        :bool(cx,false)<0?"right"
                                         :"left";
                 
 if(text)
  if(!radius){   
    if(h)    
    rotate(rot)translate([0,0,cz?-abs(h)/2:h<0?h:0]) linear_extrude(abs(h),convexity=10){
    text(str(text),size=size,halign=halign,valign=valign,font=fontstr,spacing=spacing,$fn=fn,$fs=fs);
    }
    else rotate(rot)translate([0,0,cz?-h/2:0])text(text,size=size,halign=halign,valign=valign,spacing=spacing,font=fontstr,$fn=fn,$fs=fs); 
  }
  else if (lenT){
   iRadius=radius+(cy?-txtSizeY/2:0);
    rotate(center?textmetrics?gradB(txtSizeX/2,iRadius):gradB(max(fontSize),iRadius)/2:0)
    for(i=[0:lenT-1])rotate(-gradB(fontSize[i],iRadius))
    if(h)    
    translate([0,radius,0])rotate(rot)Tz(cz?-abs(h)/2:h<0?h:0){
    %color("Chartreuse")if(viewPos&&$preview)translate([0,-1])rotate(-30)circle($fn=3);// pos Marker
    linear_extrude(abs(h),convexity=10)text(text[i],size=size,halign=true?"center":"left",valign=valign,font=fontstr,$fn=fn,$fs=fs);
    }
    else  translate([0,radius,cz?-h/2:0])rotate(rot)text(text[i],size=size,halign=true?"center":"left",valign=valign,font=fontstr,$fn=fn,$fs=fs); 
  }
    
 InfoTxt("Text",["font",font,"style",style,"trueSize",trueSizeSW,"size",str(inputSize," ⇒ ",size)],name);   
        
 HelpTxt("Text",[
"text",str("\"",text,"\""),
"size",inputSize,
"h",str(h," /*0 for 2D*/"),
"cx",cx,
"cy",cy,
"cz",cz,
"center",center,
"spacing",spacing,
"fn",fn,
"fs",fs,
"radius",radius, 
"rot",rot,
"font",str("\"",font,"\""),
"style",str("\"",style,"\""),
"name",name,
"textmetrics",textmetrics,
"viewPos",viewPos,
"trueSize",str("\"",trueSize,"\""," /* body,size,hp,cap,text,textl,font */")
],help);

 
}

 // color by color lists
module Col(no=0,alpha=1,pal=0,name=0,help){
   palette=["std","VGA","grey","pink","red","orange","yellow","brown","green","cyan","blue","violett","white","rainbow"]; 
    
HelpTxt("Col",["no",no,"alpha",alpha,"pal",pal,"name",name],help);

    for(i=[0:1:$children-1]){
    $idx=i;
    color(co[pal][(no+i)%len(co[pal])],alpha)children(i);
    union(){
      $idx=0; 
    InfoTxt("Col",["Color children ($idx)",str(i," Farb№: ",no+i,"- ",co[pal][(no+i)%len(co[pal])])," von ",len(co[pal])-1,"Palette",str(pal,"/",palette[pal],(no+i>len(co[pal])-1)?" — Out of Range":"")],name);
    }
    }
    MO(!$children);
}

/// echo color differtiations
module Echo(title,color="#FF0000",size=2,condition=true,help=false){
 idx=is_undef($idx)?false:is_list($idx)?norm($idx):$idx;
 idxON=is_undef($idxON)?false:$idxON?true:false;
 if(condition&&(!idx||idxON))
     if(version()[0]<2021)echo(str("<H",size,"><font color=",color,">",title)); 
     else if (color=="#FF0000"||color=="red")echo(str("\n🔴\t»»» ",title));
     else if (color=="redring")echo(str("\n⭕\t»»» ",title));
     else if (color=="#FFA500"||color=="orange")echo(str("\n🟠\t»»» ",title));    
     else if (color=="#00FF00"||color=="green"||color=="info")echo(str("🟢\t ",title));
     else if (color=="#0000FF"||color=="blue") echo(str("🔵\t ",title));
     else if (color=="#FF00FF"||color=="purple") echo(str("🟣\t ",title));    
     else if (color=="#000000"||color=="black") echo(str("⬤\t ",title));
     else if (color=="#FFFFFF"||color=="white") echo(str("◯\t ",title));
     else if (color=="#FFFF00"||color=="yellow"||color=="warning") echo(str("⚠\t ",title));    
         else echo(str("• ",title)); 

 HelpTxt("Echo",["title",title,"color",color,"size",size,"condition",condition],help);
}

//Clone and mirror object
module MKlon(tx=0,ty=0,tz=0,rx=0,ry=0,rz=0,mx,my,mz,help=false)
{
    mx=is_undef(mx)?sign(abs(tx)):mx;
    my=is_undef(my)?sign(abs(ty)):my;
    mz=is_undef(mz)?!mx&&!my?1:sign(abs(tz)):mz;
  
  $idx=0;  
    translate([tx,ty,tz])rotate([rx,ry,rz])children();
     
    union(){
        $helpM=0;
        $info=0; 
        $idx=1;
        $idxON=false; 
        translate([-tx,-ty,-tz])rotate([-rx,-ry,-rz])mirror([mx,my,mz]) children();
    }
    MO(!$children);
    HelpTxt("MKlon",["tx",tx,"ty",ty,"tz",tz,"rx",rx,"ry",ry,"rz",rz,"mx",mx,"my",my,"mz",mz],help);

}

// Clone and mirror (replaced by MKlon)
module Mklon(tx=0,ty=0,tz=0,rx=0,ry=0,rz=0,mx=0,my=0,mz=1)
{
    mx=tx?1:mx;
    my=ty?1:my;
    mz=tz?1:mz;
  $idx=0;
    translate([tx,ty,tz])rotate([rx,ry,rz])children(); 
    union(){
        $helpM=0;
        $info=0;
        $idx=1;
        $idxON=false;
    translate([-tx,-ty,-tz])rotate([-rx,-ry,-rz])mirror([mx,my,mz]) children(); }   
   MO(!$children);
}
//CombinedEnd from path ub_common.scad
//Combined from path utilities.scad






//A single file for all the utility modules to make the easier and cleaner to import.
//CombinedEnd from path utilities.scad
//Combined from path circle_wavy.scad


wavy_circle_demo = false;

if(wavy_circle_demo && $preview){
  #circle_wavy(r=20);
  
  circle(r=20);
  
  translate([50,0,0])
  cylinder_wavy();
}

module circle_wavy(
    r = 20,
    amplitude = 1,
    frequency = 12,
    steps = 360)
{
    assert(is_num(steps) && steps > 0, "Steps must be positive");
    assert(is_num(frequency) && frequency > 0, "Frequency must be positive");
    assert(is_num(amplitude) && amplitude >= 0, "Amplitude must be positive");
    assert(is_num(r) && r > 0, "Radius must be positive");

    if(amplitude == 0){
        circle(r=r);
    }
    else {
        outer = [
            for (i = [0:steps])
                let(
                    angle = i * 360 / steps,
                    rad = r + sin(angle * frequency) * amplitude
                )
                [ rad * cos(angle), rad * sin(angle) ]
        ];

        polygon(outer);
    }
}

module cylinder_wavy(
    r = 20,
    h = 20,
    amplitude = 1,
    frequency = 12,
    steps = 360) {

    assert(is_num(steps) && steps > 0, "Steps must be positive");
    assert(is_num(frequency) && frequency > 0, "Frequency must be positive");
    assert(is_num(amplitude) && amplitude >= 0, "Amplitude must be positive");
    assert(is_num(r) && r > 0, "r must be positive");
    assert(is_num(h) && h > 0, "h must be positive");

    linear_extrude(height=h)
      circle_wavy(
      r = r,
      amplitude = amplitude,
      frequency = frequency,
      steps = steps);
}
//CombinedEnd from path circle_wavy.scad
//Combined from path SequentialBridgingDoubleHole.scad


//sequential bridging for hanging hole. 
//ref: https://hydraraptor.blogspot.com/2014/03/buried-nuts-and-hanging-holes.html
//ref: https://www.youtube.com/watch?v=KBuWcT8XkhA

SequentialBridgingDoubleHole_demo = false;

if(SequentialBridgingDoubleHole_demo && $preview){
  $fn = 64;
  translate([0,0,0])
  SequentialBridgingDoubleHole(
    outerHoleRadius = 10,
    outerHoleDepth = 5,
    innerHoleRadius = 5,
    innerHoleDepth = 10,
    overhangBridgeCount = 2,
    overhangBridgeThickness = 0.3,
    overhangBridgeCutin = 0.05,
    magnetCaptiveHeight = 0);
    
    
  translate([25,0,0])
  SequentialBridgingDoubleHole(
    outerHoleRadius = 10,
    outerHoleDepth = 5,
    innerHoleRadius = 5,
    innerHoleDepth = 10,
    overhangBridgeCount = 2,
    overhangBridgeThickness = 0.3,
    overhangBridgeCutin = 0.05,
    magnetCaptiveHeight = 0)
    cylinder(r=10, h=$outer_height );

    translate([75,0,0])
    SequentialBridgingDoubleHole(
    outerHoleRadius = 10,
    outerHoleDepth = 5,
    innerHoleRadius = 5,
    innerHoleDepth = 10,
    overhangBridgeCount = 3,
    overhangBridgeThickness = 0.3,
    overhangBridgeCutin =0.05);

    translate([75,30,0])
    rotate([180,0,0])
    difference(){
    cylinder(h=10,r=15);
    translate([0,0,-0.01])  
    SequentialBridgingDoubleHole(
        outerHoleRadius = 10,
        outerHoleDepth = 5+0.01,
        innerHoleRadius = 5,
        innerHoleDepth = 10,
        overhangBridgeCount = 3,
        overhangBridgeThickness = 0.3,
        overhangBridgeCutin =0.05);
    }

    translate([75,60,0])
    SequentialBridgingDoubleHole(
    outerHoleRadius = 0,
    outerHoleDepth = 5,
    innerHoleRadius = 5,
    innerHoleDepth = 10,
    overhangBridgeCount = 0,
    overhangBridgeThickness = 0.3,
    overhangBridgeCutin =0.05);

    translate([75,90,0])
    rotate([180,0,0])
    difference(){
    cylinder(h=10,r=15);
    translate([0,0,-0.01])  
    SequentialBridgingDoubleHole(
        outerHoleRadius = 0,
        outerHoleDepth = 5+0.01,
        innerHoleRadius = 5,
        innerHoleDepth = 10,
        overhangBridgeCount = 0,
        overhangBridgeThickness = 0.3,
        overhangBridgeCutin =0.05);
}
}

module SequentialBridgingDoubleHole(
  outerHoleRadius = 0,
  outerHoleDepth = 0,
  innerHoleRadius = 0,
  innerHoleDepth = 0,
  overhangBridgeCount = 2,
  overhangBridgeThickness = 0.3,
  overhangBridgeCutin = 0.05, //How far should the bridge cut in to the second smaller hole. This helps support the
  magnetCaptiveHeight = 0) 
{
  fudgeFactor = 0.01;
  
  hasOuter = outerHoleRadius > 0 && outerHoleDepth >0;
  hasInner = innerHoleRadius > 0 && innerHoleDepth > 0;
  bridgeRequired = hasOuter && hasInner && outerHoleRadius > innerHoleRadius && innerHoleDepth > outerHoleDepth;
  overhangBridgeCount = bridgeRequired ? overhangBridgeCount : 0;
  overhangBridgeHeight = overhangBridgeCount*overhangBridgeThickness;
  outerPlusBridgeHeight = hasOuter ? outerHoleDepth + overhangBridgeHeight : 0;
  $outer_height = outerPlusBridgeHeight+fudgeFactor;
  
  if(hasOuter || hasInner)
  union(){
    difference(){
      if (hasOuter) {
        // move the cylinder up into the body to create internal void
        translate([0,0,magnetCaptiveHeight])
        if($children >=1){
          //translate([0,0,outerHoleDepth]);
          //cylinder(r=outerHoleRadius, h=overhangBridgeHeight+fudgeFactor);
          children(0); 
        } else { 
          cylinder(r=outerHoleRadius, h=outerPlusBridgeHeight+fudgeFactor);
        }
      }
      
      if (overhangBridgeCount > 0) {
        for(i = [0:overhangBridgeCount-1]) 
          rotate([0,0,180/overhangBridgeCount*i])
          for(x = [0:1]) 
          rotate([0,0,180]*x)
            translate([-outerHoleRadius,innerHoleRadius-overhangBridgeCutin,outerHoleDepth+overhangBridgeThickness*i])
            cube([outerHoleRadius*2, outerHoleRadius, overhangBridgeThickness*overhangBridgeCount+fudgeFactor*2]);
          }
      }
      
      if (hasInner) {
        translate([0,0,outerPlusBridgeHeight])
        cylinder(r=innerHoleRadius, h=innerHoleDepth-outerPlusBridgeHeight);
    }
  }
}
//CombinedEnd from path SequentialBridgingDoubleHole.scad
//Combined from path module_utility.scad







utility_demo = false && $preview;

if(utility_demo){
  $fn = 64;
  
  translate([400,0,0])
  union(){
    for(i = [0,1,2]){
      translate([20*i,0,0])
      bentWall(
        separation=i==1? 10 : 0,
        label_size = i==2?10:0);

      translate([20*i,100,0])
      bentWall(
        separation=i==1? 10 : 0,
        label_size = i==2?10:0, top_radius = -2);

        
      translate([20*i,200,0])
      bentWall(
        separation=i==1? 10 : 0, 
        label_size = i==2?10:0,
        thickness = [10,5]);

      translate([20*i,300,0])
      bentWall(
        separation=i==1? 10 : 0, 
        label_size = i==2?10:0,
        thickness = [10,5], top_radius = -2);
    }
  }
}

//Wall is centred on the middle of the start. Bend is not taken in to account
module bentWall(
  length=80,
  bendPosition=0,
  bendAngle=45,
  separation=20,
  lowerBendRadius=0,
  upperBendRadius=0,
  height=30,
  thickness=[10,10], //top thickness, bottom thickness
  wall_cutout_depth = 0,
  wall_cutout_width = 0,
  wall_cutout_radius = 0,
  top_radius = 0,
  label_size = 0,
  label_angle = 45,
  centred_x=true) {
  assert(is_num(thickness) || (is_list(thickness) && len(thickness) ==2), "thickness should be a list of len 2");
  fudgeFactor = 0.01;
  
  label_enabled = label_size > 0 && label_size*3 < length;
  thickness = is_num(thickness) ? [thickness,thickness] : thickness;
  thickness_bottom  = thickness.x;
  thickness_top = thickness.y;
  
  top_scale = thickness.y/thickness.x;

  top_radius = get_related_value(
    user_value = top_radius, 
    base_value = thickness_top, 
    max_value = thickness_top/2,
    default_value = 0);

  bendPosition = get_related_value(bendPosition, length, length/2);
  
  label_z_height = label_enabled ? cos(label_angle)* label_size + thickness_bottom/2 : 0;
  
  cutoutHeight = max(get_related_value(wall_cutout_depth, height, 0), label_z_height);
  cutoutRadius = label_enabled ? label_size/4 : get_related_value(wall_cutout_radius, cutoutHeight, cutoutHeight);

  label_length = length-cutoutRadius*4;
  cutoutLength = wall_cutout_width == 0 && label_enabled ? label_length : get_related_value(wall_cutout_width, length, length/2); 

  //Thickness should match the wall thickness, for tapered walls find the right position
  label_thickness = thickness_bottom-(thickness_bottom-thickness_top)*((cutoutHeight-thickness_bottom/2)/(height-thickness_bottom/2))/2;

  
  //#render()
  difference()
  {
    if(separation != 0) { 
      translate(centred_x ? [0,0,0] : [(thickness.x+separation)/2,0,0])
      translate([0,bendPosition,0])
      linear_extrude(height, scale = [top_scale,1], )
      SBogen(
        TwoD=thickness.x,
        dist=separation,
        //x0=true,
        grad=bendAngle,
        r1=lowerBendRadius <= 0 ? separation : lowerBendRadius,
        r2=upperBendRadius <= 0 ? separation : upperBendRadius,
        l1=bendPosition,
        l2=length-bendPosition);   
    } else {
      translate(centred_x ? [-thickness.x/2,0,0] : [0,0,0])
      hull(){
        rotate([90,0,0])
        translate([(thickness_bottom-thickness_top)/2,0,-length])
        roundedCube(
          size =[thickness_top, height, length],
          sideRadius = top_radius);
        cube([thickness_bottom, length, thickness_bottom/2]);
      }
    }

    //wall cutout section
    if(cutoutHeight != 0){
      translate(centred_x ? [0,0,0] : [(separation+thickness)/2+fudgeFactor,0,0])
      translate([0,length/2,height])
      rotate([0,0,90])
      WallCutout(
        height = cutoutHeight,
        lowerWidth = cutoutLength,
        cornerRadius = cutoutRadius,
        thickness = (separation+thickness[0]+fudgeFactor*2),
        topHeight = 1);
    }
  }    
  
  //wall label section
  if(label_enabled){
    label_z = height-cutoutHeight;
    label_length = cutoutLength-cutoutRadius;

    
    translate([label_thickness/2,length/2-label_length/2,0])
    hull()
    {
      translate([0,0,label_z])
      rotate([0,0,180])
      rotate([90,0,0])
      rotate_extrude(angle = 45)
      square([label_thickness,label_length]);
      //translate([0,0,label_z])
      //rotate([45,0,90])
      //cube([label_length,label_thickness,10]);
      translate([0,0,label_z])
      rotate([0,45,0])
      translate([-label_thickness,label_length,0])
      rotate([90,0,0])
      roundedCube(
          size =[label_thickness,label_size,label_length],
          sideRadius = top_radius);
    }
        
  }
}

 if(utility_demo){
 
  translate([200,0,0])
  roundedCube(
    size = [100,100,100],
    //cornerRadius=2,
    topRadius = 0, bottomRadius = 2, sideRadius = 4, 
    supportReduction_z=[-1,0],
    $fn=128);
  translate([200,150,0])
  roundedCube(
    size = [100,100,100],
    //cornerRadius=2,
    topRadius = 5, bottomRadius = 2, sideRadius = 5,
    supportReduction_x = [-1, -1],
    supportReduction_y = [-1, -1],
    supportReduction_z=[-1,0],
    $fn=128);
  translate([200,300,0])
  roundedCube(
    size = [54.5,39.5,41],
    cornerRadius=0,
    topRadius = 0, bottomRadius = 2, sideRadius = 3.75, 
    supportReduction_x = [0, 0], supportReduction_y = [0, 0], supportReduction_z = [1, 0],
    $fn=128);
}
 
//Creates a rounded cube
//x=width in mm
//y=length in mm
//z=height in mm
//cornerRadius = the radius of the cube corners
//topRadius = the radius of the top of the cube
//bottomRadius = the radius of the top of the cube
//sideRadius = the radius of the sides. This must be over 0.
module roundedCube(
  x,
  y,
  z,
  size=[],
  cornerRadius = 0,
  topRadius = 0,
  bottomRadius = 0,
  sideRadius = 0 ,
  centerxy = false,
  supportReduction_x = [0,0],
  supportReduction_y = [0,0],
  supportReduction_z = [0,0])
{
  minSideRadius = 0.01;
  assert(is_list(size), "size must be a list");
  size = len(size) == 3 ? size : [x,y,z];
  
  topRadius = topRadius > 0 ? topRadius : cornerRadius;
  bottomRadius = bottomRadius > 0 ? bottomRadius : cornerRadius;
  sideRadius = max(minSideRadius, sideRadius > 0 ? sideRadius : cornerRadius);
  
  supportReduction_z = is_num(supportReduction_z) ? [supportReduction_z, supportReduction_z] : supportReduction_z;
  supportReduction_x = is_num(supportReduction_x) ? [supportReduction_x, supportReduction_x] : supportReduction_x;
  supportReduction_y = is_num(supportReduction_y) ? [supportReduction_y, supportReduction_y] : supportReduction_y;

  assert(topRadius <= sideRadius, str("topRadius must be less than or equal to sideRadius. topRadius:", topRadius, " sideRadius:", sideRadius));
  assert(bottomRadius <= sideRadius, str("bottomRadius must be less than or equal to sideRadius. bottomRadius:", bottomRadius, " sideRadius:", sideRadius));

  //Support reduction should move in to roundedCylinder
  function auto_support_reduction(supportReduction, corner_radius, center_radius) = 
    let(center_radius = is_num(center_radius) ? center_radius : corner_radius,
      sr = (supportReduction == -1 ? corner_radius/2 : supportReduction)+max(0,center_radius-corner_radius))
    min(sr, center_radius);

  //z needs to account for the side radius as the side radius can be greater than the top and bottom radius.
  supReduction_z = [auto_support_reduction(supportReduction_z[0], bottomRadius, sideRadius), auto_support_reduction(supportReduction_z[1], topRadius, sideRadius)];
  supReduction_x = [auto_support_reduction(supportReduction_x[0], sideRadius), auto_support_reduction(supportReduction_x[1], sideRadius)];
  supReduction_y = [auto_support_reduction(supportReduction_y[0], sideRadius), auto_support_reduction(supportReduction_y[1], sideRadius)];

  //x and y need and offset to account for the top and bottom radius
  supReduction_x_offset = [auto_support_reduction(supportReduction_x[0], bottomRadius), auto_support_reduction(supportReduction_x[1], topRadius)];
  supReduction_y_offset = [auto_support_reduction(supportReduction_y[0], bottomRadius), auto_support_reduction(supportReduction_y[1], topRadius)];

  positions=[
     [[sideRadius                         ,sideRadius],                        [0,0]]
    ,[[max(size.x-sideRadius, sideRadius) ,sideRadius]                        ,[1,0]]
    ,[[max(size.x-sideRadius, sideRadius) ,max(size.y-sideRadius, sideRadius)],[1,1]]
    ,[[sideRadius                         ,max(size.y-sideRadius, sideRadius)],[0,1]]
    ];
    
  translate(centerxy ? [-size.x/2,-size.y/2,0] : [0,0,0])
  hull() 
  {
    for (i =[0:1:len(positions)-1])
    {
      translate(positions[i][0]) 
        union(){
        roundedCylinder(h=size.z,r=sideRadius,roundedr2=topRadius,roundedr1=bottomRadius);
        if(supReduction_z[1] > 0)
          translate([0,0,size.z-topRadius])
          cylinder(h=topRadius, r=supReduction_z[1]);

        if(supReduction_z[0] > 0)
          cylinder(h=bottomRadius, r=supReduction_z[0]);
        
        if(supReduction_x[0] > 0 && positions[i][1].x ==0){
          if(topRadius ==0 && bottomRadius == 0)
          {
            translate([0,0,size.z/2])
            cube(size=[sideRadius*2,supReduction_x[0]*2,size.z],center=true);
          } else {
            //bottom
            translate([0,0,supReduction_x[0]+supReduction_x_offset[0]])
            rotate([0,90,0])
            cylinder(h=sideRadius*2, r=supReduction_x[0],center=true);
            //top
            translate([0,0,size.z-supReduction_x[0]-supReduction_x_offset[1]])
            rotate([0,90,0])
            cylinder(h=sideRadius*2, r=supReduction_x[0],center=true);
          }
        }
        
        if(supReduction_x[1] > 0 && positions[i][1].x ==1){
         if(topRadius == 0 && bottomRadius == 0)
         {
            translate([0,0,size.z/2])
            cube(size=[sideRadius*2,supReduction_x[1]*2,size.z],center=true);
          } else {
            //bottom
            translate([0,0,supReduction_x[1]+supReduction_x_offset[0]])
            rotate([0,90,0])
            cylinder(h=sideRadius*2, r=supReduction_x[1],center=true);
            //top
            translate([0,0,size.z-supReduction_x[1]-supReduction_x_offset[1]])
            rotate([0,90,0])
            cylinder(h=sideRadius*2, r=supReduction_x[1],center=true);
          }
        }
        
        if(supReduction_y[0] > 0 && positions[i][1].y == 0){
            //bottom
            translate([0,0,supReduction_y[0]+supReduction_y_offset[0]])
            rotate([0,90,90])
            cylinder(h=sideRadius*2, r=supReduction_y[0],center=true);
            //top
            translate([0,0,size.z-supReduction_y[0]-supReduction_y_offset[1]])
            rotate([0,90,90])
            cylinder(h=sideRadius*2, r=supReduction_y[0],center=true);
        }
        if(supReduction_y[1] > 0 && positions[i][1].y == 1){
            //bottom
            translate([0,0,supReduction_y[1]+supReduction_y_offset[0]])
            rotate([0,90,90])
            cylinder(h=sideRadius*2, r=supReduction_y[1], center=true);
            //top
            translate([0,0,size.z-supReduction_y[1]-supReduction_y_offset[1]])
            rotate([0,90,90])
            cylinder(h=sideRadius*2, r=supReduction_y[1], center=true);
        }
      }
    }
  }
}

//Creates a rounded cube
//x=width in mm
//y=length in mm
//z=height in mm
//cornerRadius = the radius of the cube corners
module roundedCubeV1(
  x,
  y,
  z,
  cornerRadius)
{
  positions=[
     [cornerRadius                      ,cornerRadius                      ,cornerRadius]
    ,[max(x-cornerRadius, cornerRadius) ,cornerRadius                      ,cornerRadius]
    ,[max(x-cornerRadius, cornerRadius) ,max(y-cornerRadius, cornerRadius) ,cornerRadius]
    ,[cornerRadius                      ,max(y-cornerRadius, cornerRadius) ,cornerRadius]
    ];

  hull(){
    for (x =[0:1:len(positions)-1])
    {
      translate(positions[x]) 
        sphere(cornerRadius);
      translate(positions[x]) 
        cylinder(z-cornerRadius,r=cornerRadius);
    }
  }
}

if(utility_demo){

roundedCorner(
  radius = 10, 
  length = 100, 
  height = 25,
  $fn=128); 
}
//create a negative rouneded corner that subtracted from a shape
//radius = the radius of the corner 
//length = the extrusion/length
//height = the distance past the corner.
module roundedCorner(
  radius = 10, 
  length, 
  height)
{
  assert(is_num(length), "length must be a number");
  assert(is_num(height), "height must be a number");
  assert(is_num(radius), "radius must be a number");
  difference(){
    union(){
      //main corner to be removed
      translate([0,-radius, -radius])
        cube([length, radius*2,  radius*2]);
      //corner extension in y
      translate([0,0, -radius])
        cube([length, height, radius]);
      //corner extension in x
      translate([0,-radius, 0])
        cube([length, radius, height]);
    }
    translate([-1,radius, radius])
      rotate([90, 0, 90])
      cylinder(h = length+2, r=radius);
  }  
}

if(utility_demo){
  
translate([0,50,0])
chamferedCorner(
  chamferLength = 10, 
  cornerRadius = 4, 
  length=100, 
  height=25,
  width = 20,
  $fn=128);
}
  
//create a negative chamfer corner that subtracted from a shape
//chamferLength = the amount that will be subtracted from the 
//cornerRadius = the radius of the corners 
//length = the extrusion/length
//height = the distance past the corner
module chamferedCorner(
  chamferLength = 10, 
  cornerRadius = 4, 
  length, 
  height,
  width = 0,
  angled_extension = false)
{
  fudgeFactor = 0.01;
  width = width>0 ? width : chamferLength;
 
  difference(){
    union(){
      //main corner to be removed
      translate([0,-width, -width])
        cube([length, chamferLength+width,  chamferLength+width]);
      //corner extension in y
      translate([0,chamferLength-fudgeFactor, -width])
        rotate_around_point(point=[0,0,width], rotation=angled_extension ? [-45,0,0] : [0,0,0])
        cube([length, height-chamferLength, width]);
      //corner extension in x
      translate([0,-width, chamferLength-fudgeFactor])
        rotate_around_point(point=[0,width,0], rotation=angled_extension ? [45,0,0] : [0,0,0])
        cube([length, width, height-chamferLength]);

    }
    hull(){
      positions = [
        [-1,chamferLength, cornerRadius],
        [-1,cornerRadius, chamferLength],
        [-1,chamferLength, chamferLength]];
      for(i=[0:len(positions)-1])
      {
        translate(positions[i])
          rotate([90, 0, 90])
          cylinder(h = length+2, r=cornerRadius);
      }
    }
  }        
}

module rotate_around_point(point=[], rotation=[]){
  translate(point)
  rotate(rotation)
  translate(-point)
  children();
}




if(utility_demo){
  
translate([-100,0,0])
CubeWithRoundedCorner(
  $fn=128);
translate([-100,20,0])
CubeWithRoundedCorner(
  edgeRadius = 2,
  $fn=128);
}

//Creates a cube with a single rounded corner.
//Centered around the rounded corner
module CubeWithRoundedCorner(
  size=[10,10,10], 
  cornerRadius = 5, 
  edgeRadius = 0,
  center=false){
  assert(is_list(size) && len(size)==3, "size should be a list of size 3");
  assert(is_num(cornerRadius) && cornerRadius >= 0, "cornerRadius should be a number greater than 0");
  assert(is_num(edgeRadius), "edgeRadius should be a number");
  
  fudgeFactor = 0.01;
  
  translate(center ? -size/2 : [0,0,0])
  if(edgeRadius <=0) {
    hull(){
      translate([cornerRadius,cornerRadius,0])
      cylinder(r=cornerRadius, h=size.z+fudgeFactor);
      translate([cornerRadius,0,0])
        cube([size.x-cornerRadius,size.y,size.z+fudgeFactor]);
      translate([0,cornerRadius,0])
        cube([size.x,size.y-cornerRadius,size.z+fudgeFactor]);
    }
  }
  else{
    hull(){
      translate([cornerRadius,cornerRadius,0])
      roundedCylinder(h=size.z+fudgeFactor,r=cornerRadius,roundedr2=edgeRadius);
      
      translate([(size.x+cornerRadius)/2,size.y/2,size.z/2])
      rotate([0,90,0])
      CubeWithRoundedCorner(
        size=[size.z,size.y,size.x-cornerRadius], 
        cornerRadius = edgeRadius,
        edgeRadius=0,
        center=true);
        
      translate([size.x/2,(size.y+cornerRadius)/2,size.z/2])
      rotate([0,90,270])
      CubeWithRoundedCorner(
        size=[size.z,size.y,size.x-cornerRadius], 
        cornerRadius = edgeRadius,
        edgeRadius=0,
        center=true);        
    }
  }
}

module roundedCylinder(h,r,roundedr=0,roundedr1=0,roundedr2=0)
{
  assert(is_num(h), "h must have a value");
  assert(is_num(r), "r must have a value");
  roundedr1 = roundedr1 > 0 ? roundedr1 : roundedr;
  roundedr2 = roundedr2 > 0 ? roundedr2 : roundedr;
  
  assert(is_num(roundedr1), "roundedr1 or roundedr must have a value");
  assert(is_num(roundedr2), "roundedr2 or roundedr must have a value");
  
  if(roundedr1 > 0 || roundedr2 > 0){
    hull(){
      if(roundedr1 > 0)
        roundedDisk(r,roundedr1,half=-1);
      else
        cylinder(r=r,h=h-roundedr2);
        
      if(roundedr2 > 0)
        translate([0,0,h-roundedr2*2]) 
          roundedDisk(r,roundedr2,half=1);
      else
        translate([0,0,roundedr1]) 
          cylinder(r=r,h=h-roundedr1);
    }
  }
  else {
    cylinder(r=r,h=h);
  }
}

module roundedDisk(r,roundedr, half=0){
 hull(){
    translate([0,0,roundedr]) 
    rotate_extrude() 
    translate([r-roundedr,0,0])
    difference(){
      circle(roundedr);
      //Remove inner half so we dont get error when r<roundedr*2
      translate([-roundedr*2,-roundedr,0])
      square(roundedr*2);
      
      if(half<0){
        //Remove top half
        translate([-roundedr,0,0])
        square(roundedr*2);   
      }
      if(half>0){
        //Remove bottom half
        translate([-roundedr,-roundedr*2,0])
        square(roundedr*2);   
      }
    }
  }
}

module tz(z) {
  translate([0, 0, z]) children();
}
//rounded_taper();
module rounded_taper(
  upperRadius=35,
  upperLength=20,
  lowerRadius=10,
  lowerLength=20,
  transitionLength=10,
  cornerRadius=0,
  roundedUpper=false,
  roundedLower=false,
  alignTop = false) {
 
  bottomWidth = lowerRadius*2;
  //topWidth = lowerWidth+(height/tan(wallAngle))*2;
  topWidth = upperRadius*2;
  height = upperLength+transitionLength+lowerLength;
  
  translate([0,0,alignTop?-height:0])
  rotate_extrude(angle=360, convexity=10)
  intersection(){
    square([topWidth,height]);
    
    //Use triple offset to fillet corners
    //https://www.reddit.com/r/openscad/comments/ut1n7t/quick_tip_simple_fillet_for_2d_shapes/
    offset(r=-cornerRadius)
    offset(r=2 * cornerRadius)
    offset(r=-cornerRadius)
    union(){
      hull(){
        //upper
        translate([-topWidth/2,lowerLength+transitionLength])
          square([topWidth,upperLength+(roundedUpper?0:cornerRadius)]);
        //transition
        translate([-bottomWidth/2,lowerLength])
          square([bottomWidth,transitionLength]);
      }
      //lower
      translate([-bottomWidth/2,roundedLower?0:-cornerRadius])
      square([bottomWidth,lowerLength+(roundedLower?0:cornerRadius)]);
    }
  }
}

module PartialCylinder(h, r, part) {
    rotate_extrude(angle = part)
        square([r, h]);
}
//CombinedEnd from path module_utility.scad
//Combined from path ub_sbogen.scad






// works from OpenSCAD version 2021 or higher   maintained at https://github.com/UBaer21/UB.scad

/** \mainpage
 * ##Open SCAD library www.openscad.org 
 * **Author:** ulrich.baer+UBscad@gmail.com (mail me if you need help - i am happy to assist)
*/


minVal=0.0000001; // minimum für nicht 0
pivotSize=$vpd/15;

function Hypotenuse(a,b)=sqrt(pow(a,2)+pow(b,2));
function hypotenuse(a,b)=sqrt(pow(a,2)+pow(b,2));
function Kathete(hyp,kat)=sqrt(pow(hyp,2)-pow(kat,2));
function kathete(hyp,kat)=sqrt(pow(hyp,2)-pow(kat,2));

function Hexstring(c)=str("#",Hex(c[0]*255),Hex(c[1]*255),Hex(c[2]*255));

// two digit dec max 255
function Hex(dec)= 
    let(
    dec=min(abs(dec),255),
    sz=floor(dec/16),
    s1=floor(dec)-(sz*16)
    )
    str(sz>14?"F":
        sz>13?"E":
        sz>12?"D":
        sz>11?"C": 
        sz>10?"B":
        sz>9?"A":sz,      
        s1>14?"F":
        s1>13?"E":
        s1>12?"D":
        s1>11?"C": 
        s1>10?"B":
        s1>9?"A":s1   
  
    );

function RotLang(rot=0,l=10,l2,z,e,lz)=let(
rot=is_undef(rot)?0:rot%360,
l=is_undef(l)?0:l,
l2=is_undef(l2)?l:l2,
lz=is_undef(lz)?l:lz
)
is_undef(z)?is_undef(e)?[sin(rot)*l,cos(rot)*l2]:
                        [sin(rot)*cos(e%360)*l,cos(rot)*cos(e%360)*l2,sin(e%360)*lz]:
            [sin(rot)*l,cos(rot)*l,z];

/** \page Functions \name kreis
kreis() generates points on a circle or arc
\param r radius
\param rand dist second radius
\param grad angle
\param grad2 angle second arc
\param fn fragments
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
